LucoseGlucose/ASC-Farm-Robot/Solidworks/MS24 Arm.SLDPRT

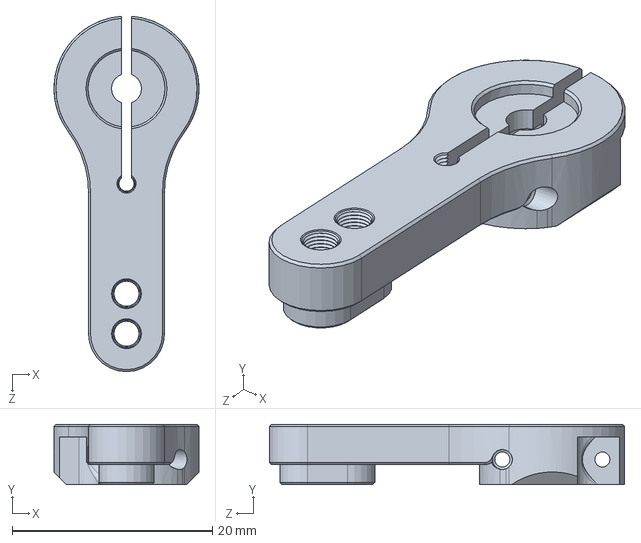
[picture p17: CAD file, 2026-04-16]
Solidworks/MS24 Arm.SLDPRT
14.5 x 6.00 x 35.5 mm
